dave2/ntpstick/src/ntpstick/console.h

#ifndef CONSOLE_H_INCLUDED
#define CONSOLE_H_INCLUDED

/* Copyright (C) 2014 David Zanetti
 *
 * This file is part of ntpstick
 *
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
 * If not, see <http://www.gnu.org/licenses/>.
 */

/** \brief Modes that a console session can operate in */
typedef enum {
    ch_mode_serial = 0, /**< Serial mode */
    ch_mode_telnet, /**< Telnet mode */
} ch_mode_t;

/** \brief Open a console channel, given an stdio handle for it
 *
 *  This will initalise the buffers and associate the given file
 *  handle with the channel.
 *
 *  \param chanid What channel number to open (0-n)
 *  \param stream Pointer to the stdio stream to read/write from
 *  \param mode Mode to operate this console in
 *  \return 0 on success, libkakapo/errors.h otherwise
 */
int console_open(uint8_t chanid, FILE *stream, ch_mode_t mode);

/** \brief Close the channel.
 *
 *  This ensures any writes to the channel are discarded properly.
 *
 *  \param chanid What channel number to close (0-n)
 *  \return 0 on success, libkakapo/errors.h otherwise
 */
int console_close(uint8_t chanid);

/** \brief Process characters coming in for a channel
 *
 *  This should be called on a regular basis, or when the lower level
 *  has indicated it has characters.
 *
 *  \param chanid What channel number to process (0-n)
 *  \return 0 on sucess, libkakapo/errors.h otherwise
 */
int console_process(uint8_t chanid);

/** \brief Set the prompt to be used for accepting commands
 *
 *  This is what is used as the command line prompt for the console.
 *  The whole prompt must be provided, there are no implied characters
 *  added to the end (ie, no shell indicator or space)
 *
 *  \param chanid What channel number this is set on (0-n)
 *  \param prompt String to use as a prompt.
 *  \return 0 on success, libkakapo/errors.h otherwise
 */
int console_set_prompt(uint8_t chanid, char *prompt);

/** \brief Prompt for a command
 *
 *  This is the step which actually outputs the prompt and begins to
 *  accept commands. The actual command processing takes place in
 *  console_process().
 *
 *  \param chanid What channel to accept a command on
 *  \return 0 on success, libkakapo/errors.h otherwise
 */
int console_prompt(uint8_t chanid);

/** \brief Output a log message to the console
 *
 *  This erases the current line output, puts the log messages and
 *  the restores the command state (if any)
 *
 *  \param chanid What channel to output log to
 *  \param message Message string to post
 *  \return 0 on success, libkakapo/errors.h otherwise
 */
int console_message(uint8_t chanid, char *message);

void console_version(FILE *where);

#endif // CONSOLE_H_INCLUDED
