dave2/ntpstick/src/ntpstick/max580x.h

#ifndef MAX580X_H_INCLUDED
#define MAX580X_H_INCLUDED

/* Copyright (C) 2015 David Zanetti
 *
 * This file is part of ntpstick
 *
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
 * If not, see <http://www.gnu.org/licenses/>.
 */

/* \file
 * \brief MAX5803/5804/5805 I2C DAC driver
 *
 * All use the same protocol, but are 8, 10, or 12 bit precsion.
 * Precision is hidden such that a 16-bit value is written and
 * only top n bits are considered. Therefore we accept 16-bit
 * values for the DAC setting */

/** \brief Initalise a MAX580x
 *
 * This ensures the DAC is detected correctly and may report type
 *
 * \param port Which I2C port to use
 * \param addr The bottom two address select bits (NOT the full adddress)
 * \return 0 on success, errors.h otherwise
 */
int max580x_init(twi_portname_t port, uint8_t addr);

/** \brief Set the DAC to a specific value
 *
 * Pass a 16-bit value to the DAC to set as output. Note that the actual
 * precision will be less than this determined by the device type. The
 * top n bits are used for actual DAC setting, so the full range is 0-0xffff
 * regardless of precision.
 *
 * \param port Which I2C port to use
 * \param addr The bottom two address select bits (NOT the full address)
 * \param value The 16-bit value to set to the DAC to
 * \return 0 on success (readback from DAC), errors.h otherwise
 */
int max580x_set(twi_portname_t port, uint8_t addr, uint16_t value);

/** \brief Read the current DAC value
 *
 * This returns the 16-bit value of the *actual* DAC output, not the buffered
 * DAC registers (which may or may not have been pushed into the DAC output
 * yet. Low bits will be set to 0 where precision is not provided for them.
 *
 * \param port Which I2C port to use
 * \param addr The bottom two address select bits (NOT the full address)
 * \return 16-bit current DAC output value
 */
uint16_t max580x_read(twi_portname_t port, uint8_t addr);

#endif // MAX580X_H_INCLUDED
